AchcarLucas/Flow-Control-System/Brainstorm/macro-idea-2026-03-23.png

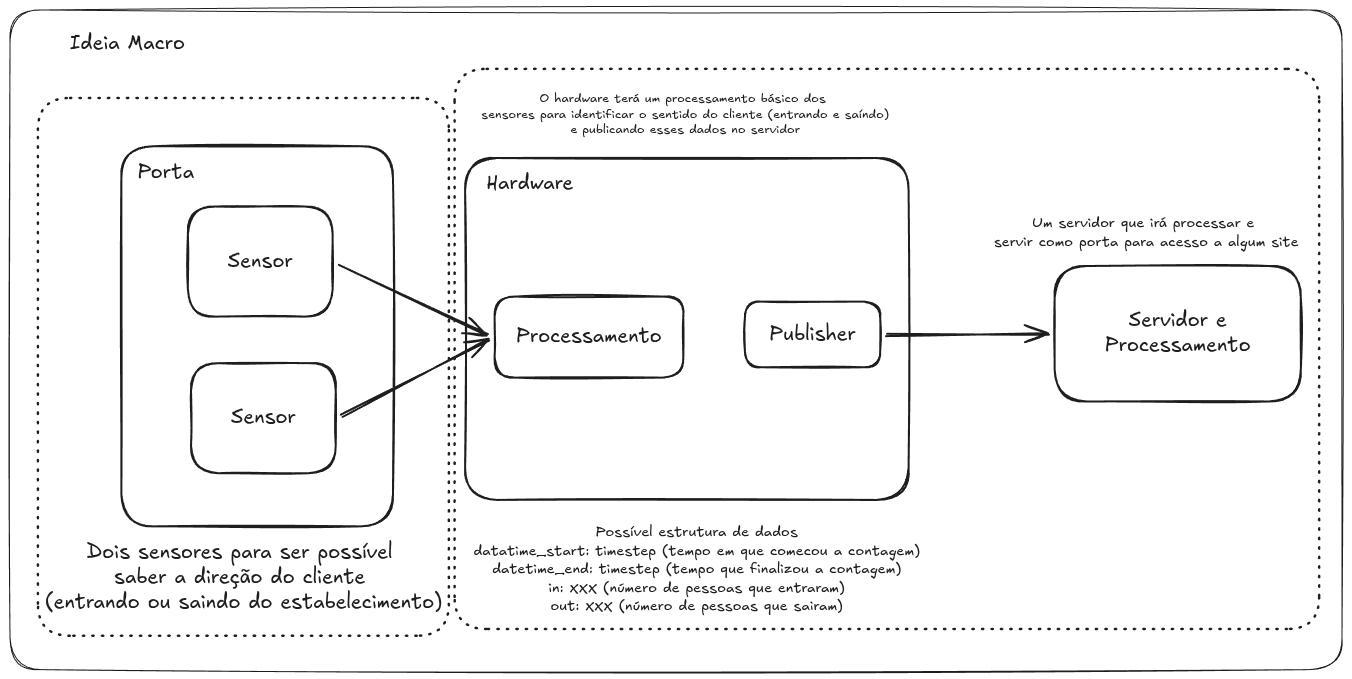
Brainstorm/macro-idea-2026-03-23.png
