AchcarLucas/Flow-Control-System/Hardware - Aspecto Geral (Diagrama de Blocos)/block-diagram-hardware-flow-control-system-2026-03-23.png

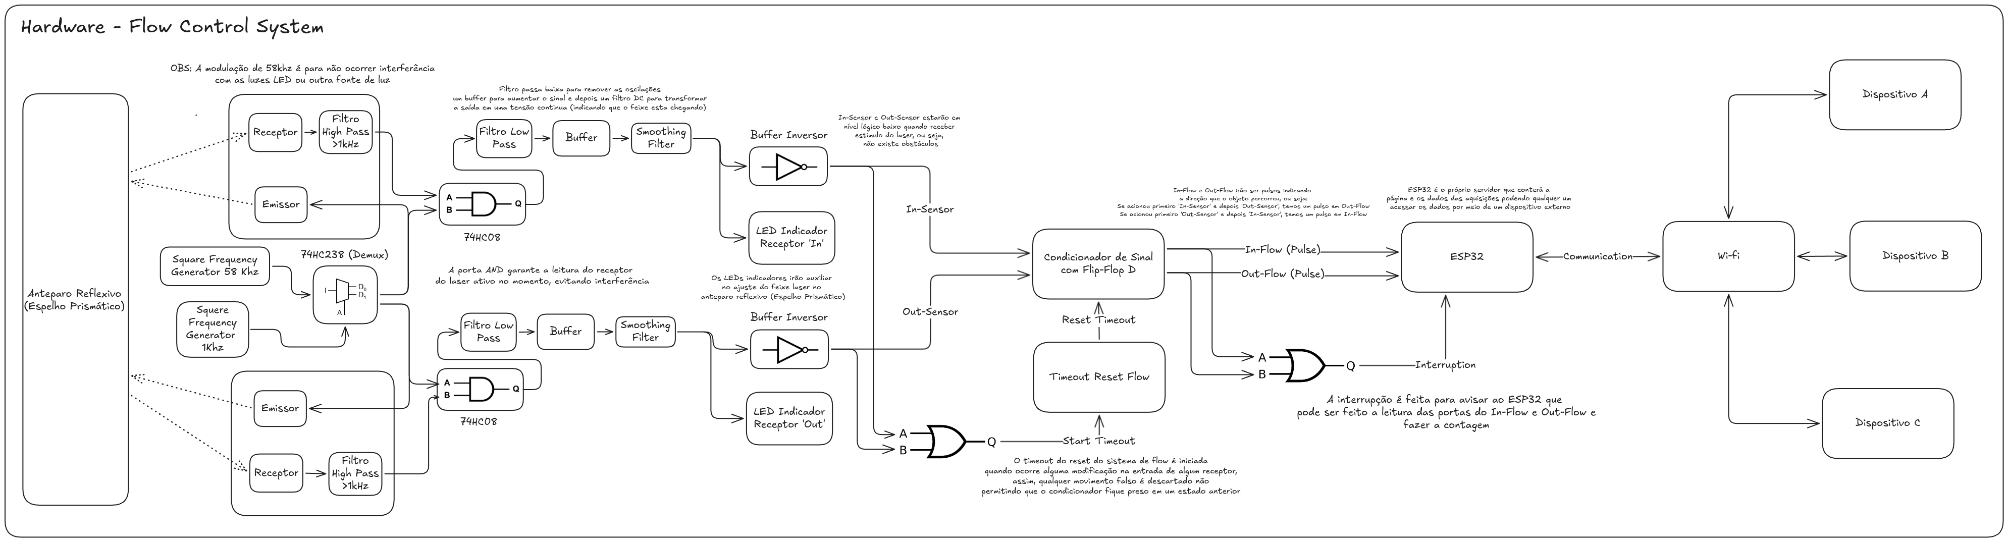
Hardware - Aspecto Geral (Diagrama de Blocos)/block-diagram-hardware-flow-control-system-2026-03-23.png
