AchcarLucas/Flow-Control-System/Building Blocks/Signal Acquisition Circuit/555-50pct-duty.png

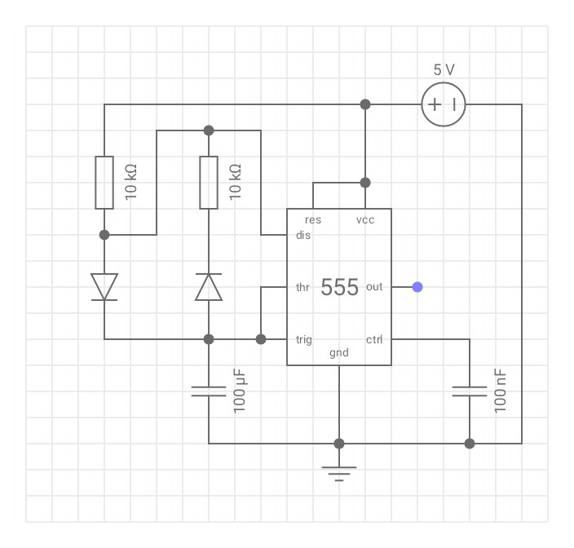
Building Blocks/Signal Acquisition Circuit/555-50pct-duty.png
