AchcarLucas/Flow-Control-System/Building Blocks/Emitter and Receiver/Buffer-KY-008/ltspace-buffer-ky-008.asc

KY_R_Inter: res; 91R
Laser: res; 75
Q1: npn; BC547B
R1: res; 10k
V1: voltage; 5V
V_Sign: voltage; PULSE(0 5 10u 1p 1p 1m 2m)
Named nets: 0
.tran 5m
