AchcarLucas/Flow-Control-System/Building Blocks/Emitter and Receiver/Polarization-TIL78/ltspace-polatization-TIL78.asc

Q1: npn; BC547B
R1: res; 200R
V1: voltage; PULSE(0 3.5 10u 1p 1p 9us 18us)
V2: voltage; 5V
Named nets: F_Sign, 0
.tran 10m
