AchcarLucas/Flow-Control-System/LTSpice/LPF.asc

C1: cap; 33nF
D1: diode
R1: res; 1k
R2: res; 10k
R3: res; 100k
S1: sw; C_SW
V1: voltage; PULSE(0 5 0 1n 1n 8.6us 17.2us)
V2: voltage; PULSE(0 5 0 1n 1n 0.5m 1m)
Named nets: 0, high_signal, low_signal
.tran 10m
.model C_SW SW(Ron=0.01 Roff=1Meg Vt=1)
